skogaby/KFChickenShim/Images/1.JPEG

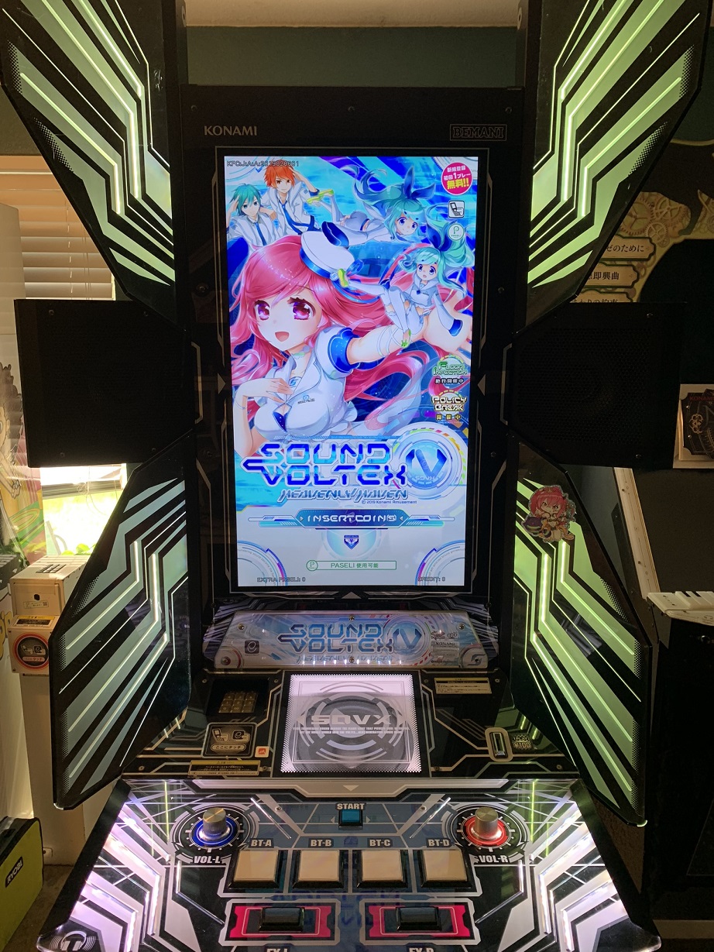
Images/1.JPEG
